BrianEnigma/3D-Cat_Food_Toy/catfoodtoy-triangles.png

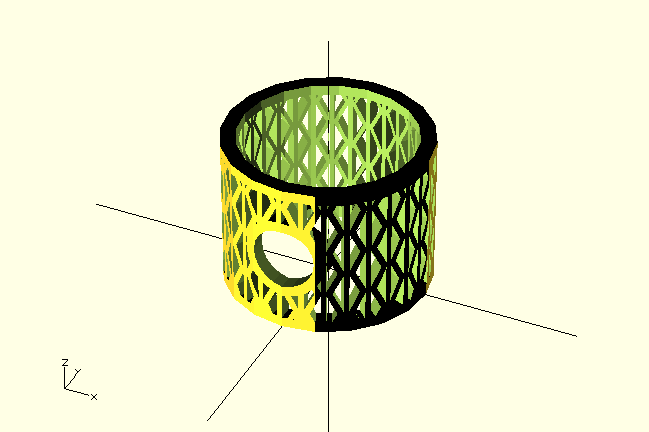
catfoodtoy-triangles.png
