BrianEnigma/3D-Cat_Food_Toy/catfoodtoy-triangles-sample_print.jpg

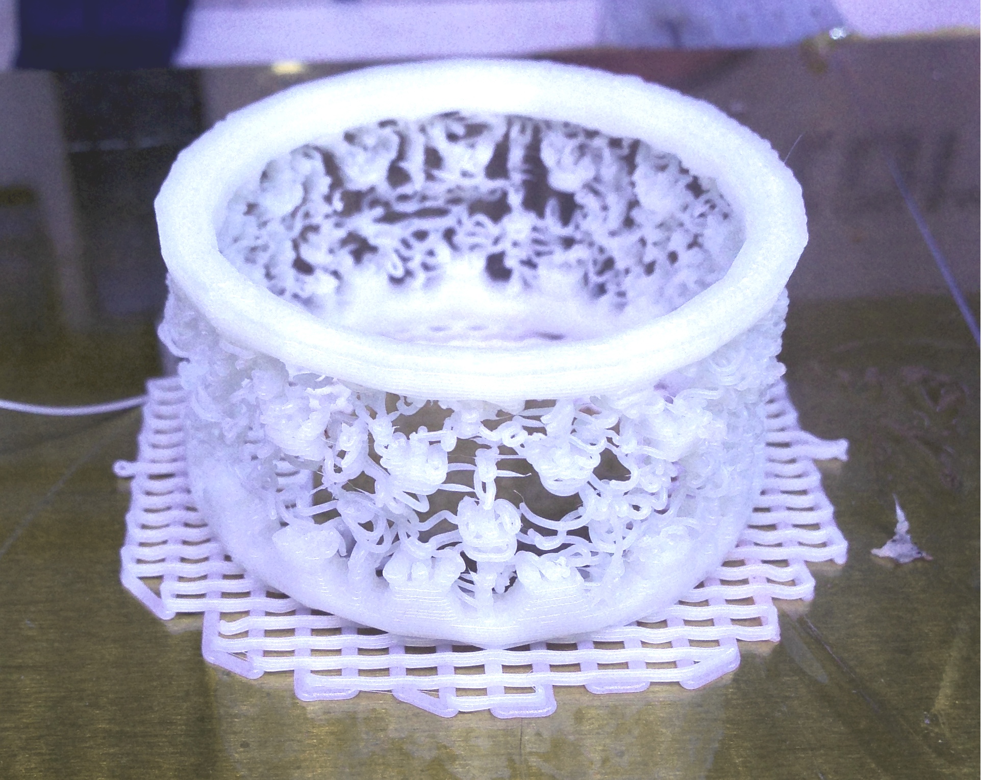
catfoodtoy-triangles-sample_print.jpg
